swaziloo/cinque/images/cinque0005.jpg

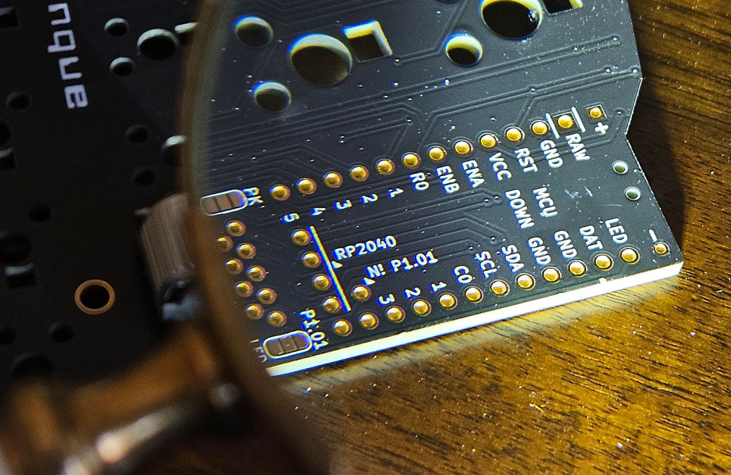
images/cinque0005.jpg
