swaziloo/cinque/images/cinque0006.jpg

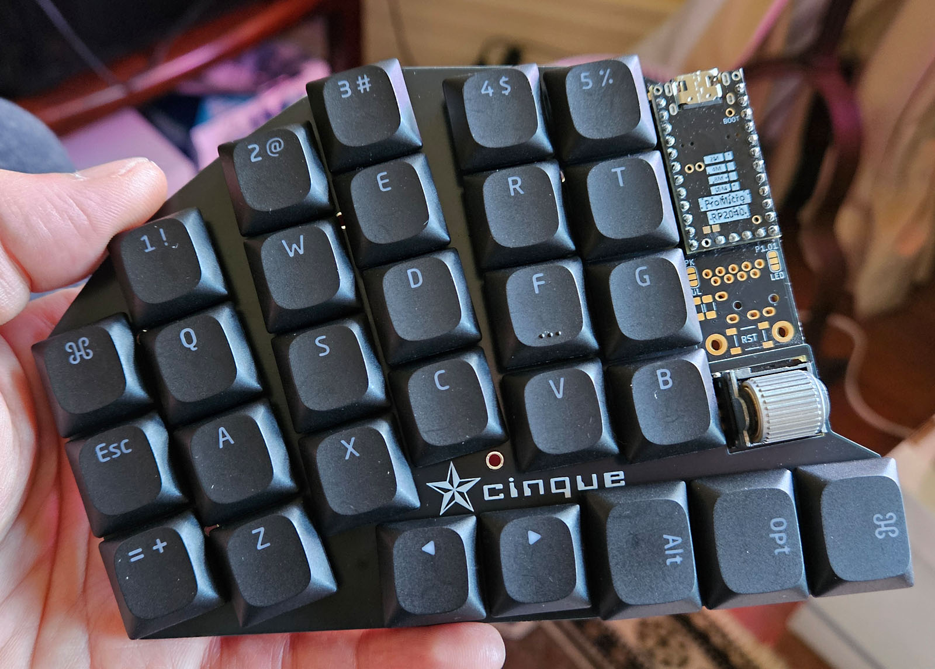
images/cinque0006.jpg
