swaziloo/cinque/images/cinque0007.jpg

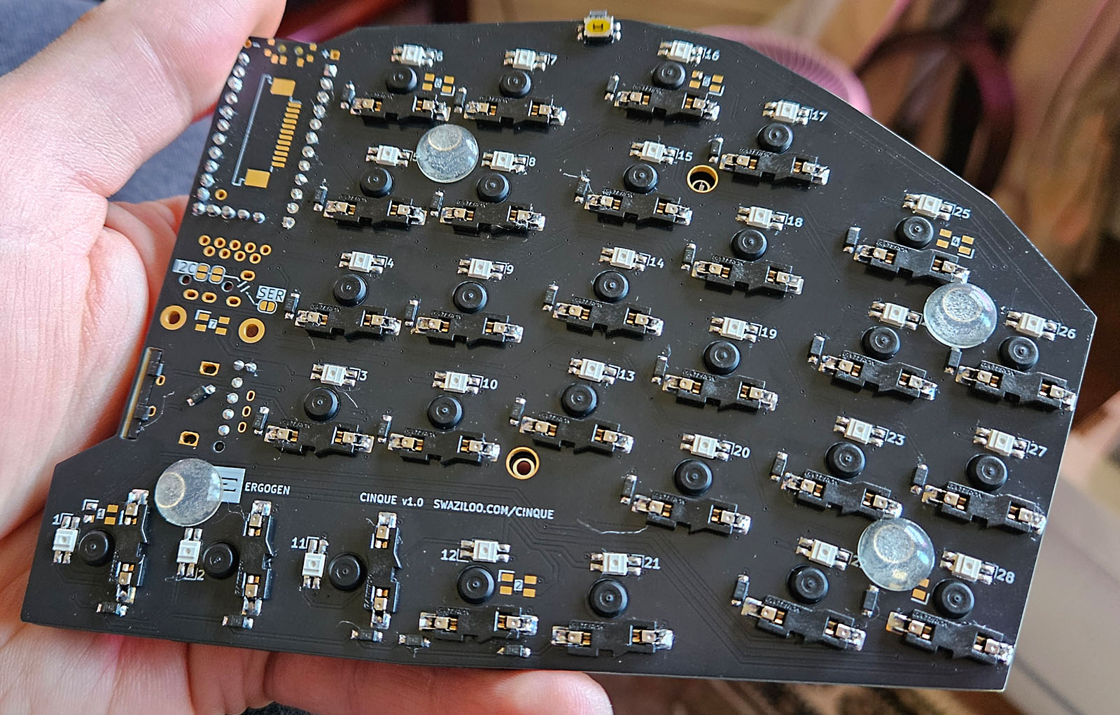
images/cinque0007.jpg
