swaziloo/cinque/images/cinque0009.jpg

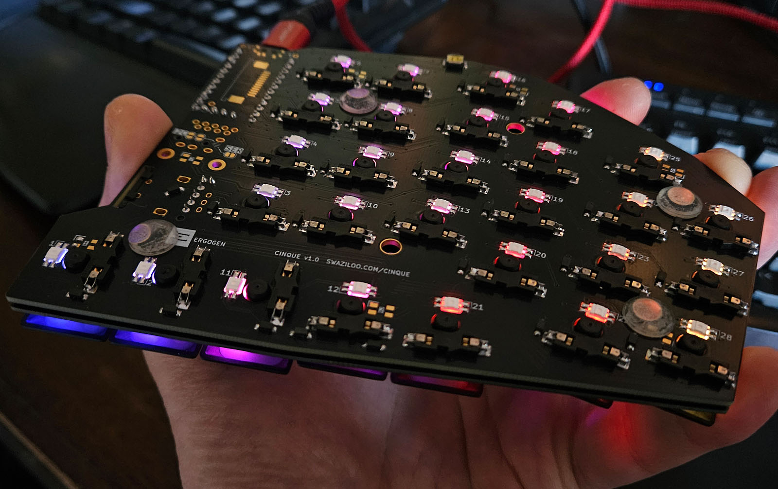
images/cinque0009.jpg
