swaziloo/cinque/images/cinque0010.jpg

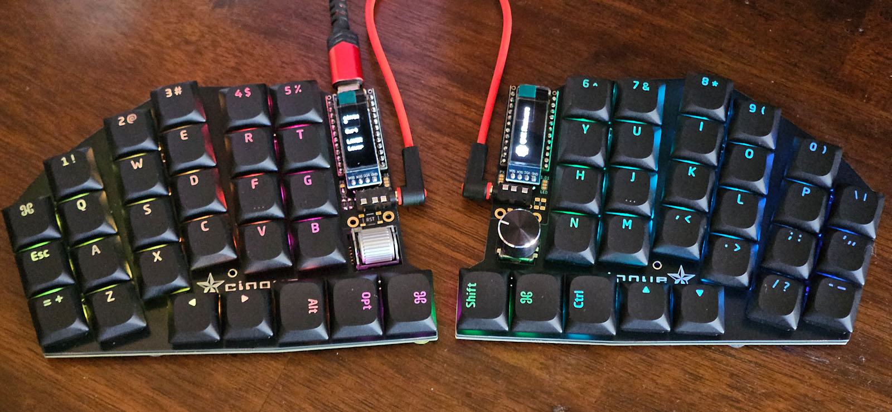
images/cinque0010.jpg
