swaziloo/cinque/images/cinque0012.jpg

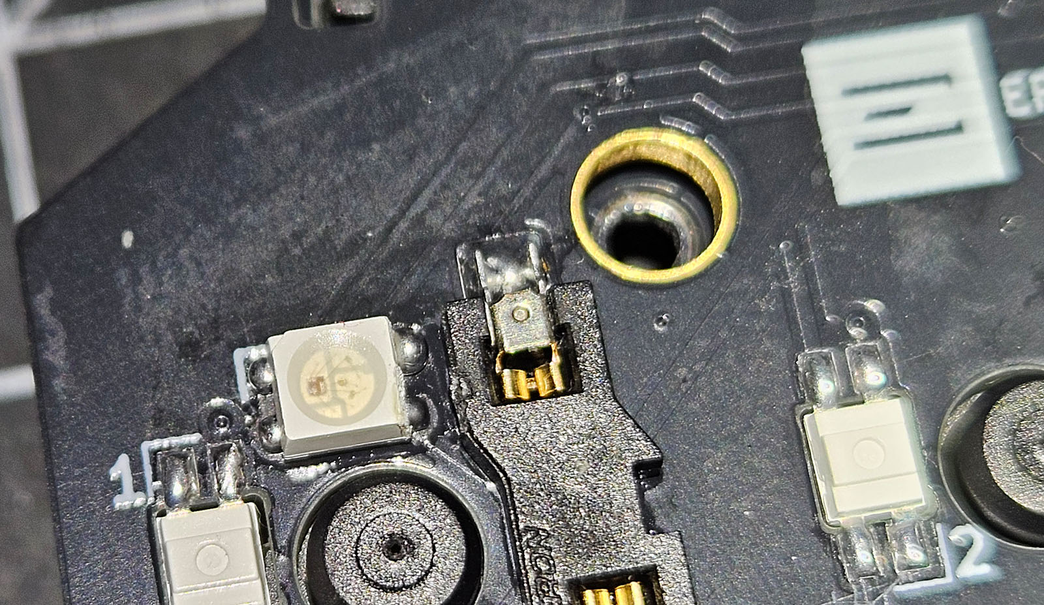
images/cinque0012.jpg
