swaziloo/cinque/images/cinque0013.jpg

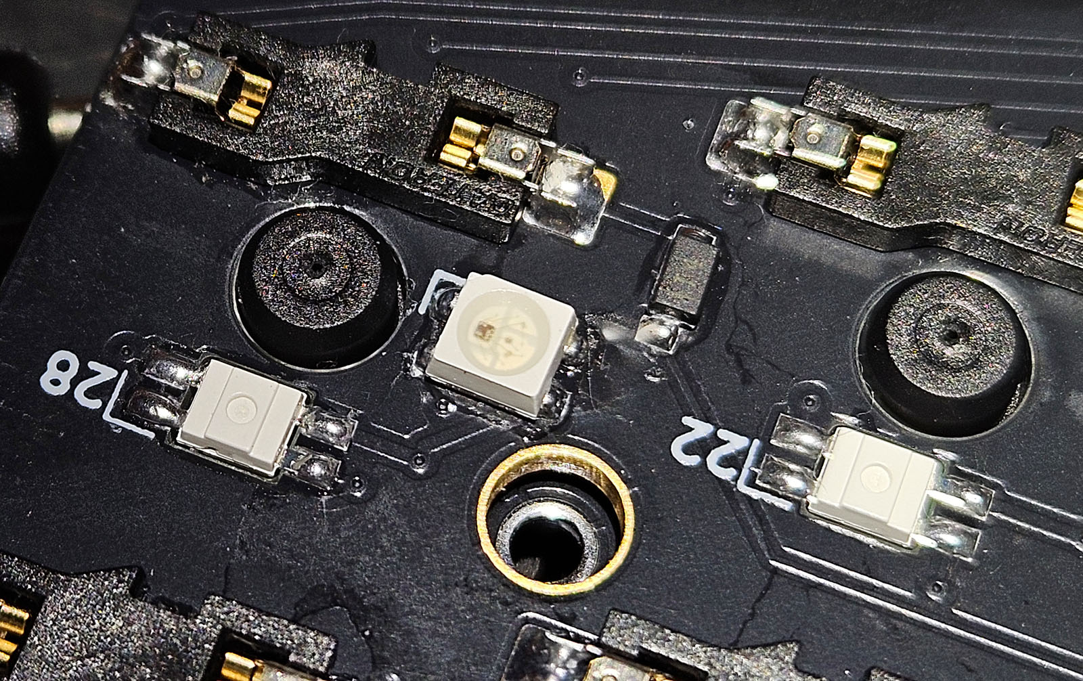
images/cinque0013.jpg
