swaziloo/cinque/images/cinque0021.jpg

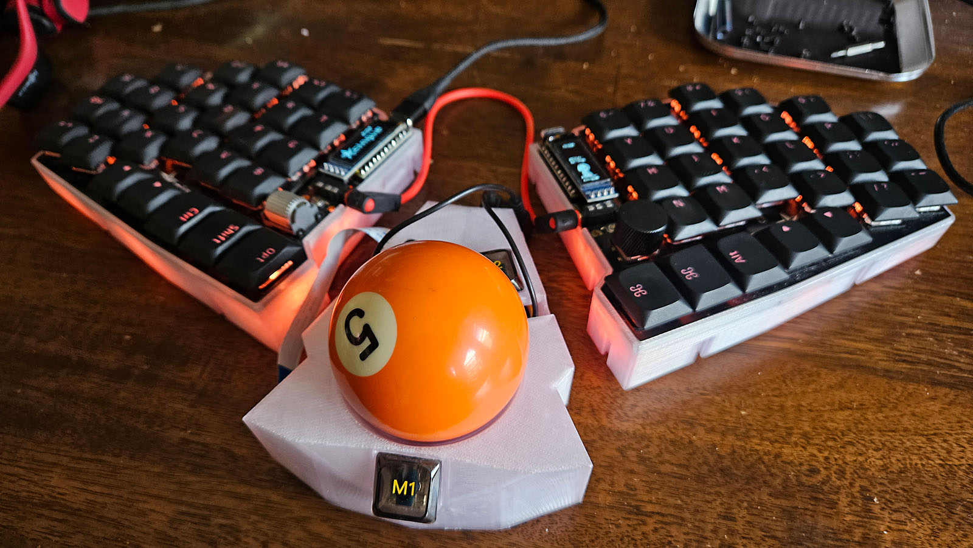
images/cinque0021.jpg
