swaziloo/cinque/images/cinque0022.jpg

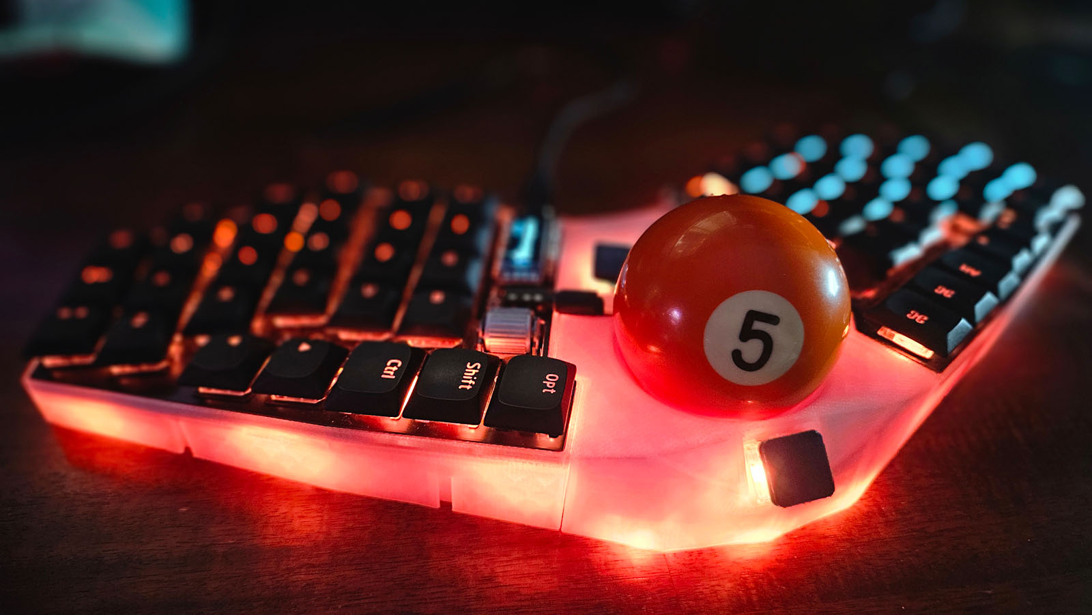
images/cinque0022.jpg
