swaziloo/cinque/images/cinque0024.jpg

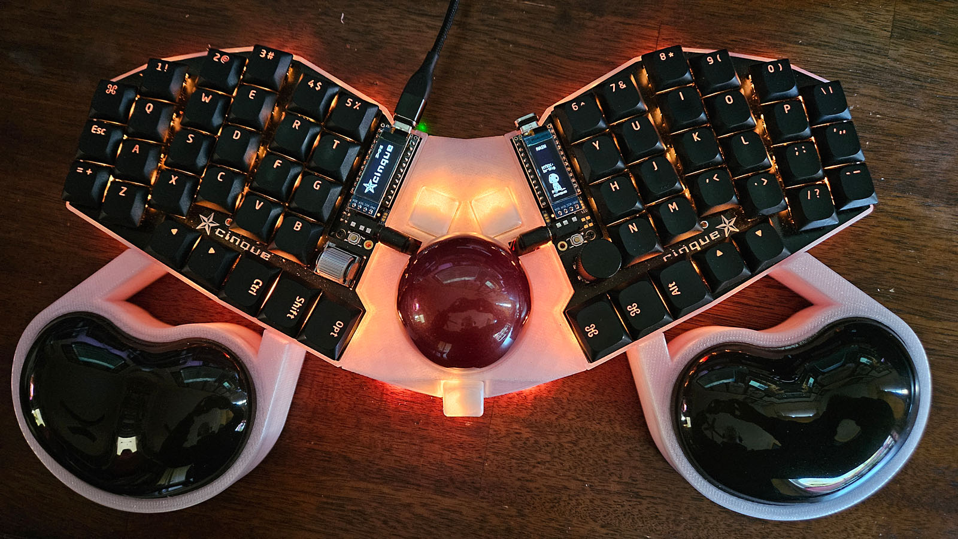
images/cinque0024.jpg
