swaziloo/cinque/images/cinque0028.jpg

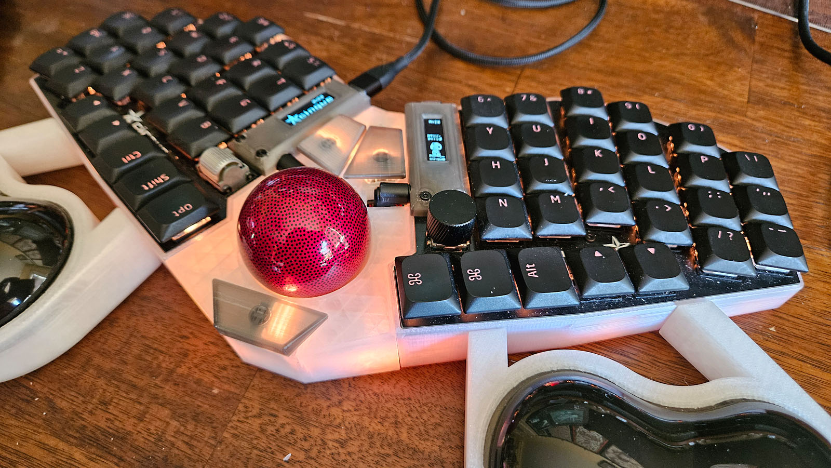
images/cinque0028.jpg
