swaziloo/cinque/images/cinque0029.jpg

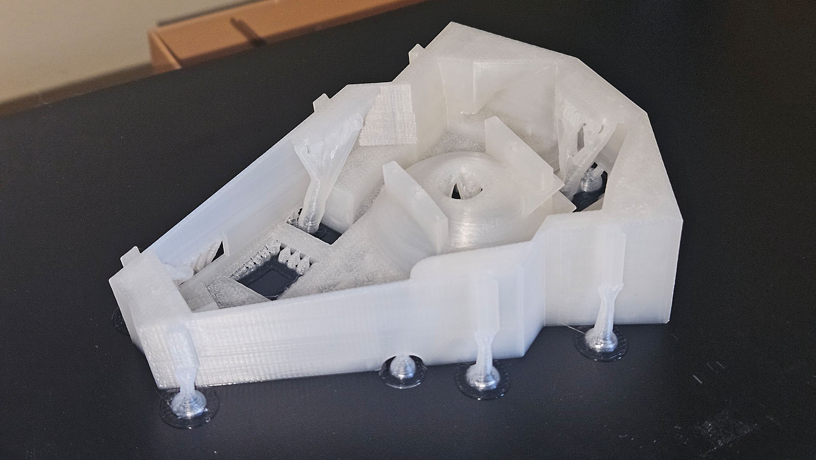
images/cinque0029.jpg
