swaziloo/cinque/images/cinque0032.jpg

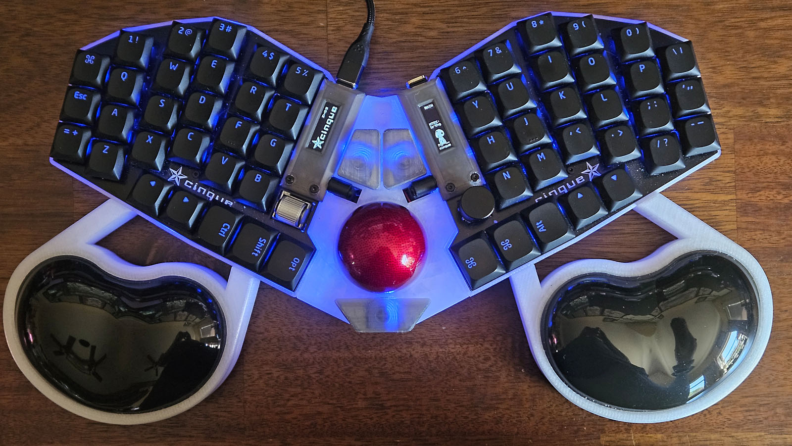
images/cinque0032.jpg
