swaziloo/cinque/images/cinque0036.jpg

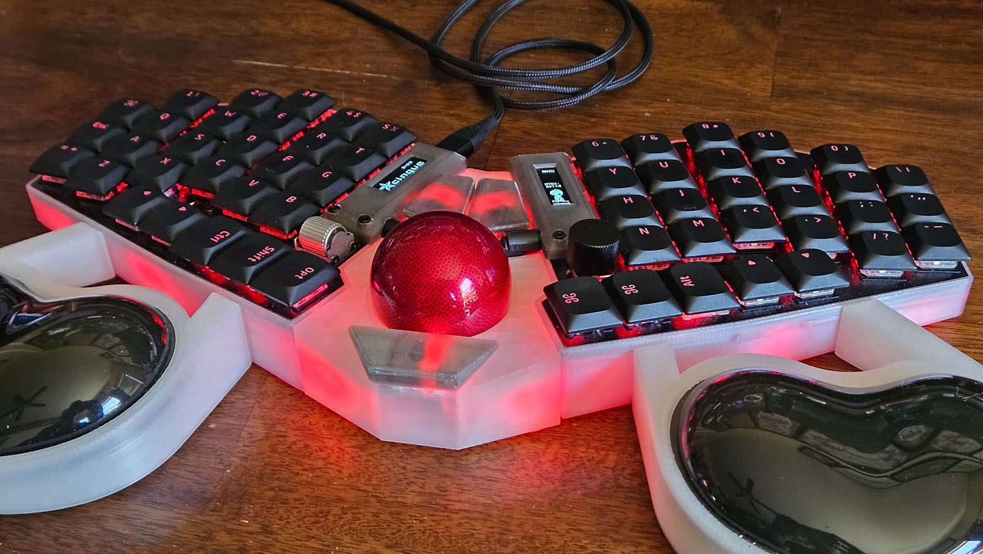
images/cinque0036.jpg
