swaziloo/cinque/images/cinque0046.jpg

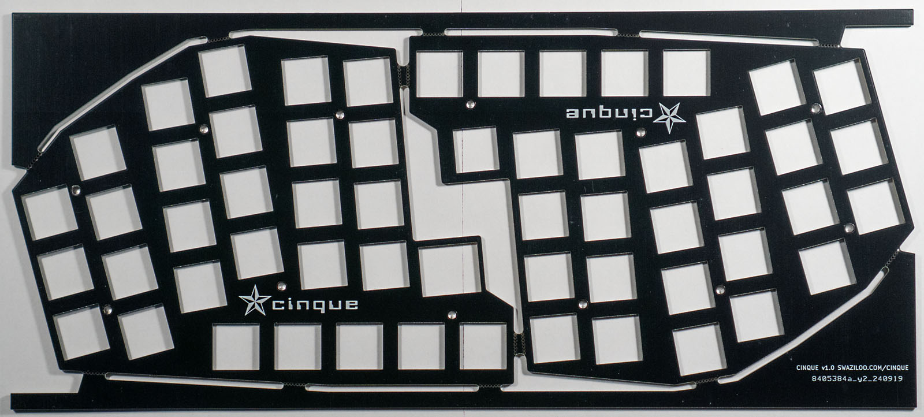
images/cinque0046.jpg
