swaziloo/cinque/images/cinque0047.jpg

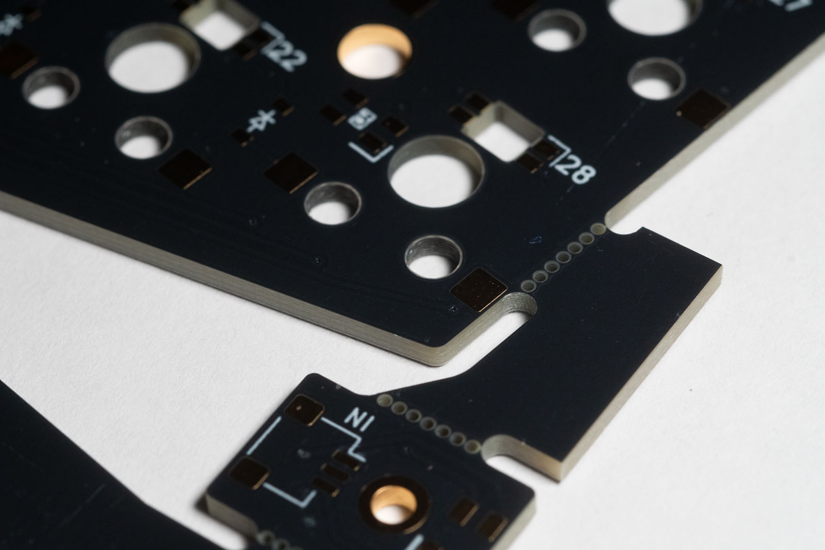
images/cinque0047.jpg
