swaziloo/cinque/images/cinque0050.jpg

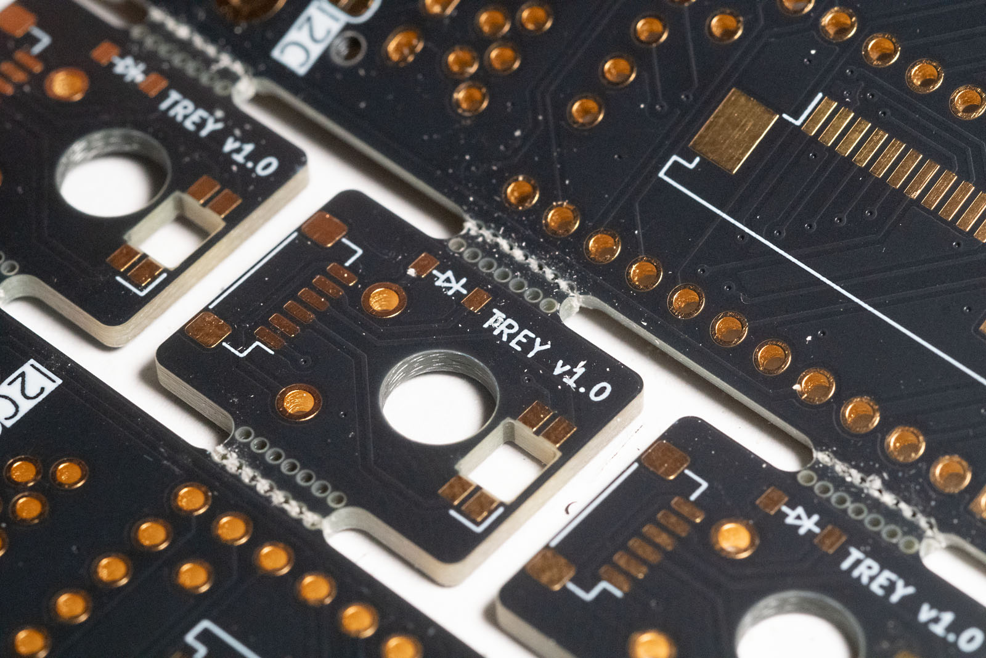
images/cinque0050.jpg
