swaziloo/cinque/images/cinque0053.jpg

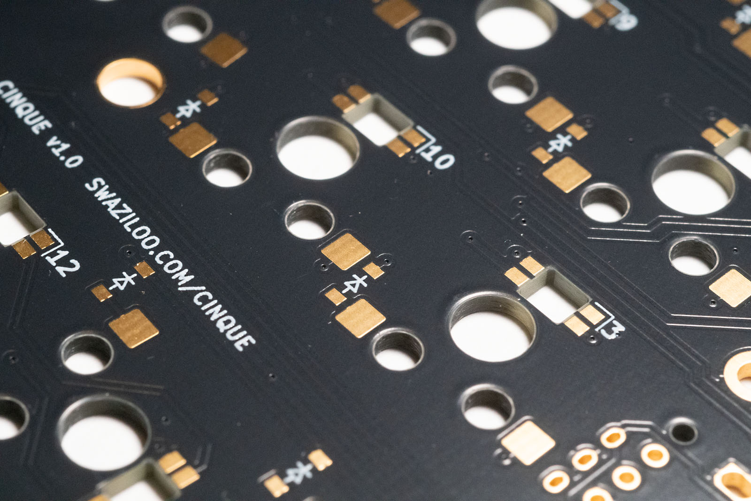
images/cinque0053.jpg
