swaziloo/cinque/case/stl/cinque-1.0-connector-b.stl

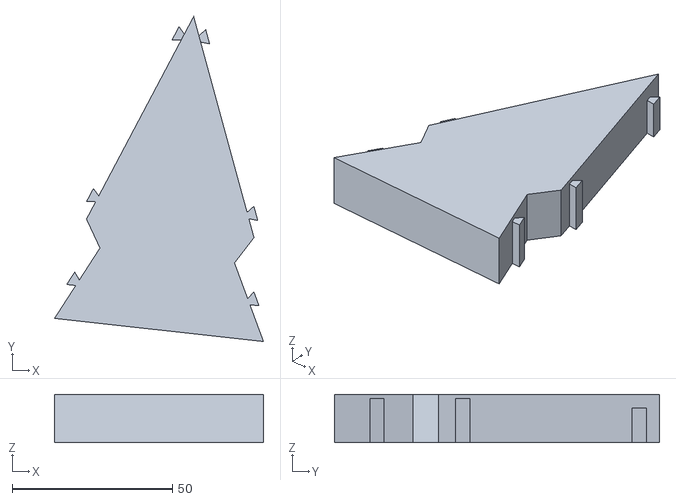
[picture p69: CAD file, 2025-06-13]
case/stl/cinque-1.0-connector-b.stl
65.2 x 101.4 x 15.0
